GaudiLabs/OpenThereminV4/Software/Open_Theremin_V4/theremin_sintable4.c

/* Theremin WAVE Table "Sinus" - 1024 entries full table, amplitude -2048.,*/

#include <avr/pgmspace.h>

const int16_t sine_table4[1024] PROGMEM = {\

0,
3,
8,
16,
24,
32,
43,
47,
47,
47,
54,
54,
54,
58,
62,
69,
69,
69,
77,
77,
81,
84,
92,
92,
92,
92,
100,
100,
107,
111,
115,
115,
130,
134,
137,
137,
152,
160,
160,
175,
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
};
