GaudiLabs/OpenThereminV4/Software/Open_Theremin_V4/theremin_sintable5.c

/* Theremin WAVE Table "Sinus" - 1024 entries full table, amplitude -2048,*/

#include <avr/pgmspace.h>

const int16_t sine_table5[1024] PROGMEM = {\
0,
76,
83,
83,
98,
98,
106,
110,
113,
128,
128,
144,
144,
144,
159,
166,
174,
181,
193,
196,
211,
219,
227,
234,
242,
249,
257,
257,
257,
279,
291,
294,
302,
310,
317,
325,
347,
352,
357,
362,
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
};
