GaudiLabs/OpenThereminV4/Software/Open_Theremin_V4/theremin_sintable7.c

/* Theremin WAVE Table "Sinus" - 1024 entries full table, amplitude -2048.,*/

#include <avr/pgmspace.h>

const int16_t sine_table7[1024] PROGMEM = {\
11,
42,
47,
51,
56,
62,
68,
73,
79,
106,
220,
235,
258,
269,
281,
296,
326,
341,
356,
371,
379,
386,
409,
416,
424,
439,
462,
467,
472,
477,
499,
511,
522,
537,
545,
552,
560,
571,
582,
605,
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

};
