GaudiLabs/OpenThereminV4/Software/Open_Theremin_V4/theremin_sintable8.c

/* Theremin WAVE Table "Sinus" - 1024 entries full table, amplitude -2048.,*/

#include <avr/pgmspace.h>

const int16_t sine_table8[1024] PROGMEM = {\
11,
42,
47,
51,
56,
69,
80,
91,
102,
112,
123,
130,
138,
145,
152,
159,
166,
174,
181,
188,
195,
202,
210,
217,
224,
231,
238,
246,
253,
260,
267,
274,
282,
289,
297,
304,
312,
327,
334,
342,
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
};
